matthewfrazier/pillbox/pillbox_presentation.png

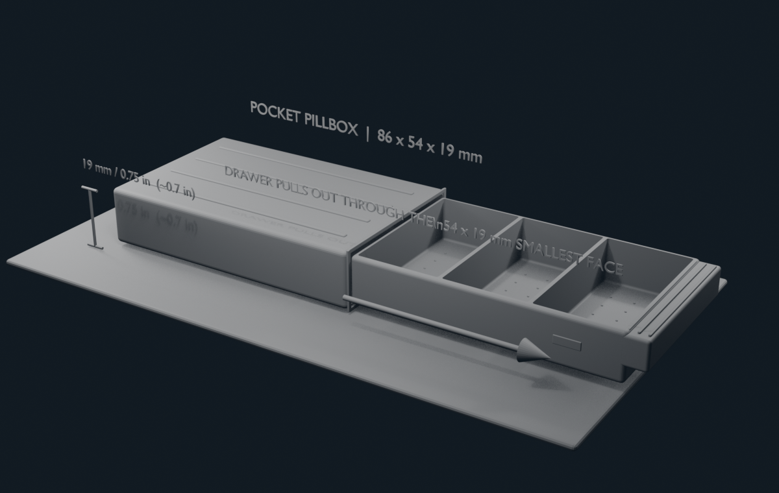
pillbox_presentation.png
