matthewfrazier/pillbox/pillbox_v6_edge_roller_mechanism.png

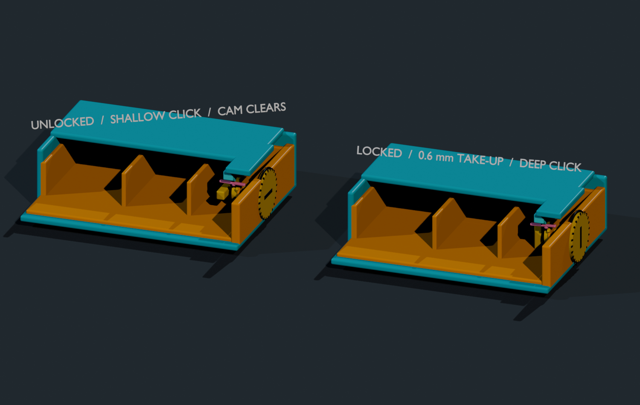
pillbox_v6_edge_roller_mechanism.png
