matthewfrazier/pillbox/v4_animation_frames/frame_0001.png

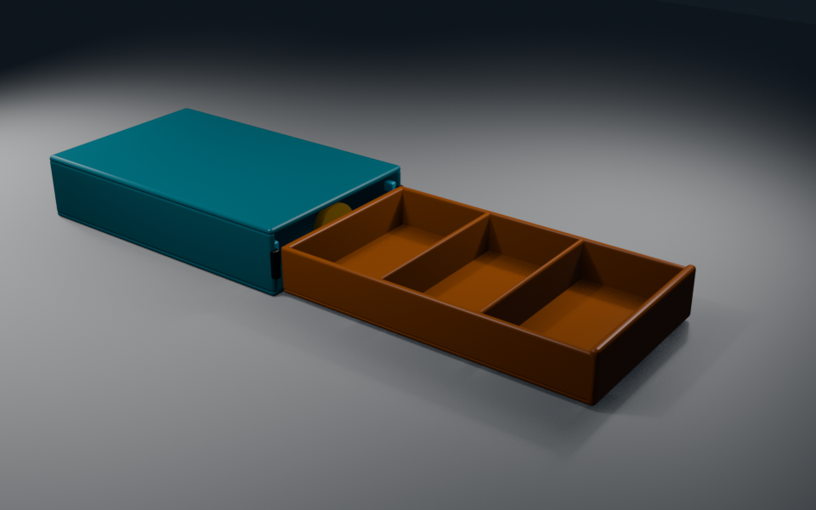
v4_animation_frames/frame_0001.png
