matthewfrazier/pillbox/v4_animation_frames/frame_0005.png

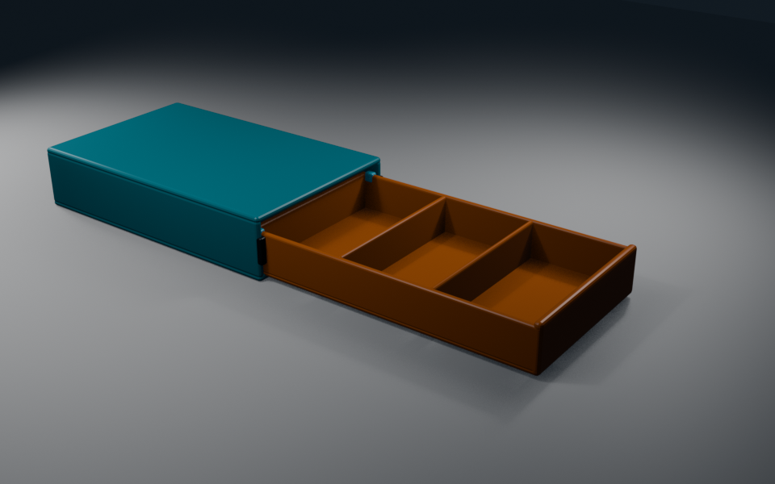
v4_animation_frames/frame_0005.png
