matthewfrazier/pillbox/v4_animation_frames/frame_0008.png

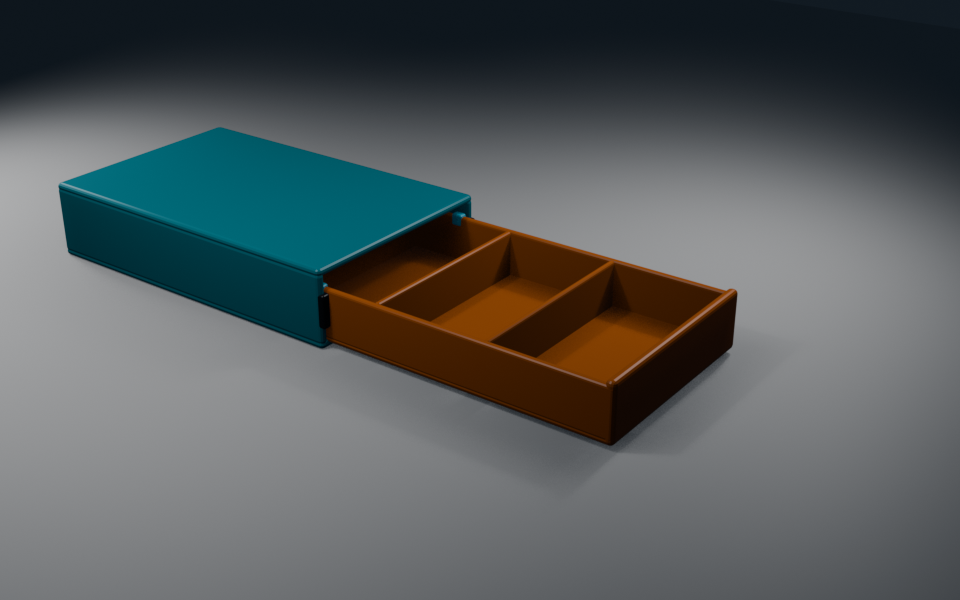
v4_animation_frames/frame_0008.png
