matthewfrazier/pillbox/v4_animation_frames/frame_0009.png

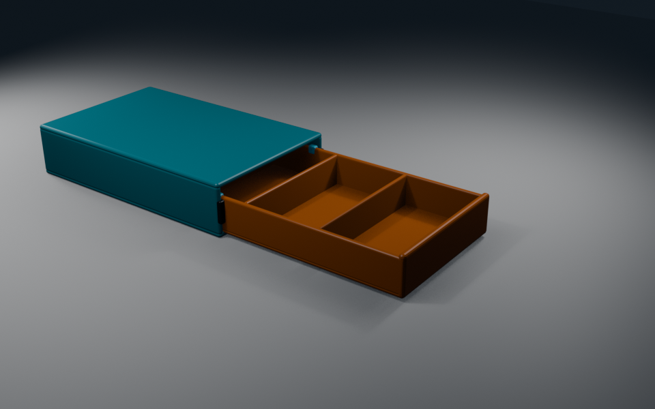
v4_animation_frames/frame_0009.png
