matthewfrazier/pillbox/v4_animation_frames/frame_0011.png

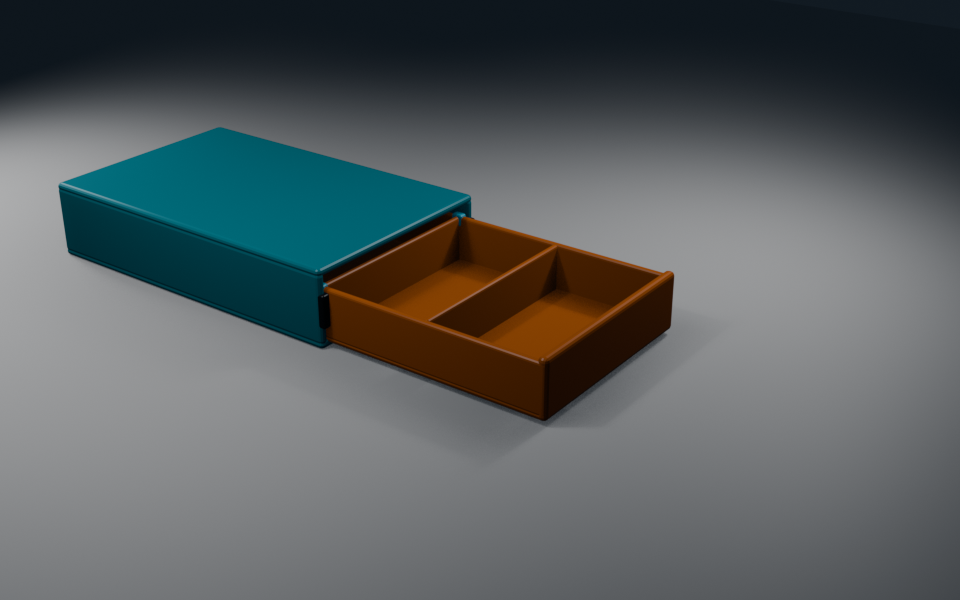
v4_animation_frames/frame_0011.png
