matthewfrazier/pillbox/v4_animation_frames/frame_0014.png

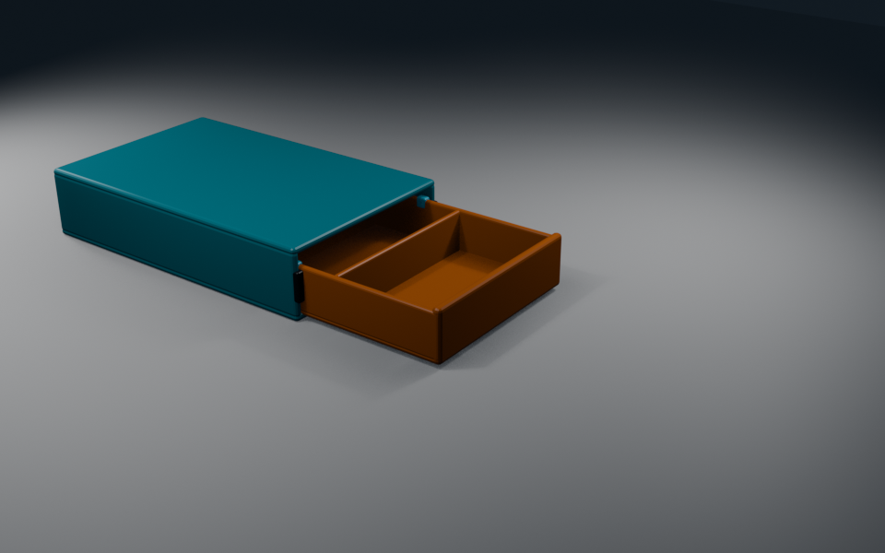
v4_animation_frames/frame_0014.png
