matthewfrazier/pillbox/v4_animation_frames/frame_0016.png

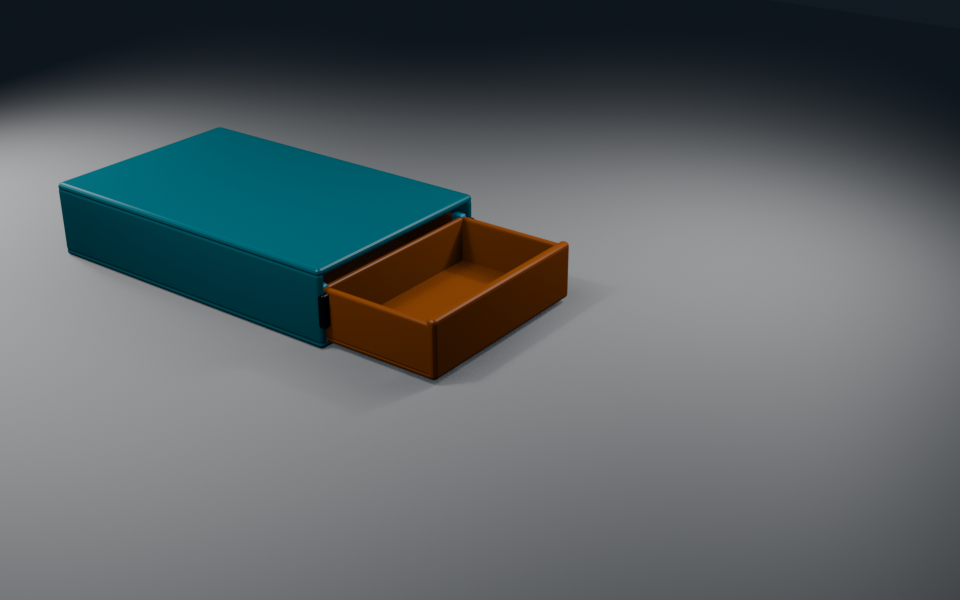
v4_animation_frames/frame_0016.png
