matthewfrazier/pillbox/pillbox_v6_edge_roller_inventory_top.png

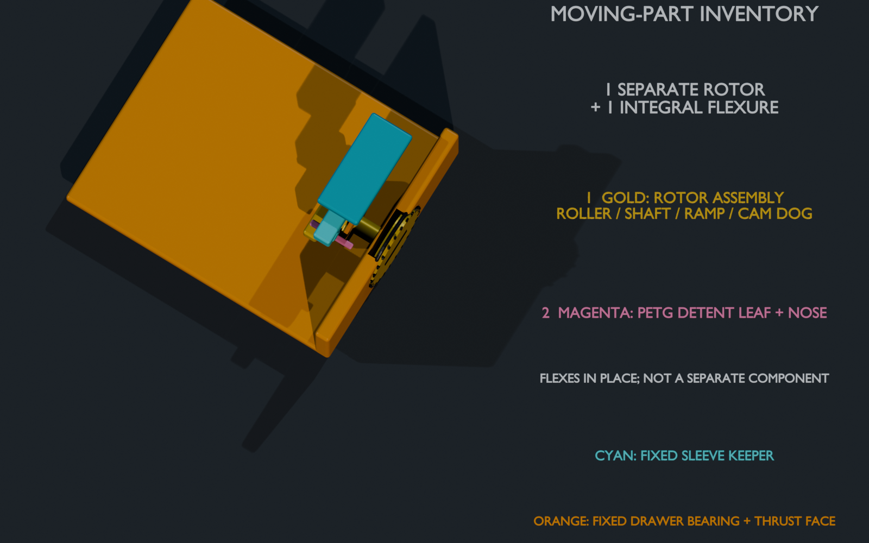
pillbox_v6_edge_roller_inventory_top.png
