matthewfrazier/pillbox/pillbox_v6_print_layout_plan.png

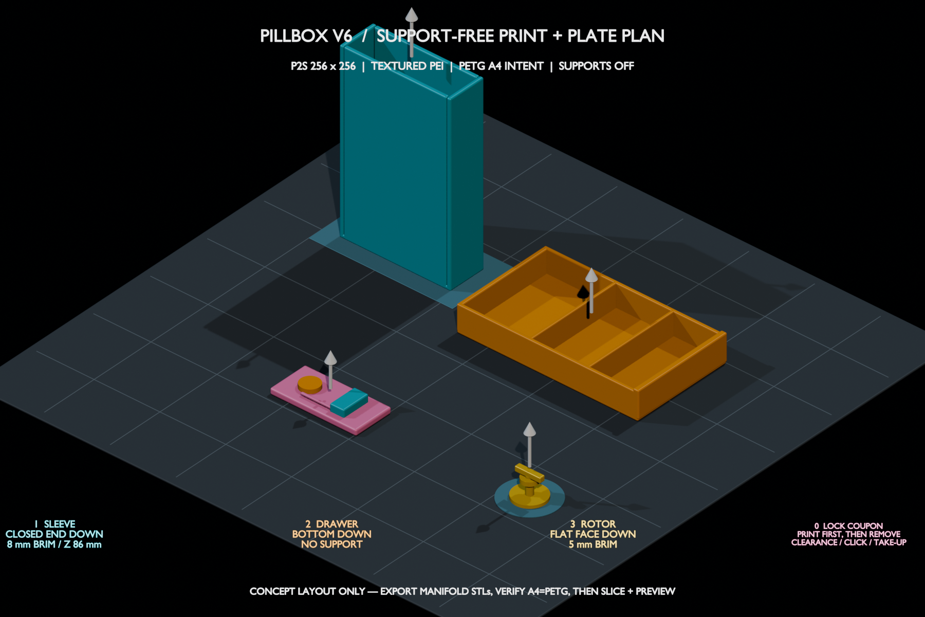
pillbox_v6_print_layout_plan.png
